diydoohickeys/Rackglow/docs/images/panel-colour.jpg

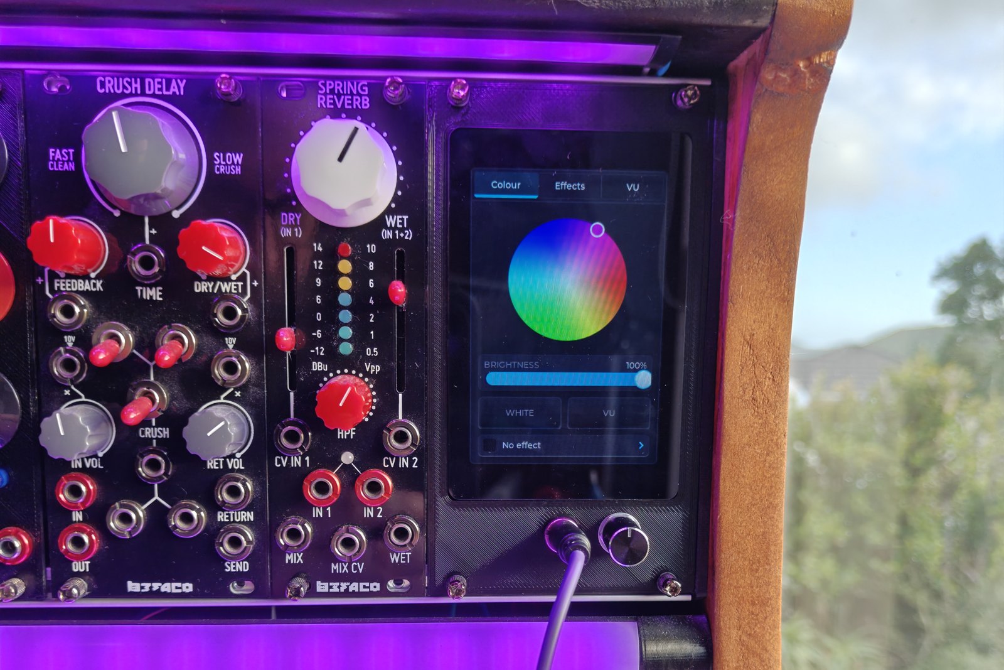
docs/images/panel-colour.jpg
