diydoohickeys/Rackglow/hardware/rackglow.kicad_sch

## KiCad design hardware/rackglow.kicad_sch (2026-09-21)

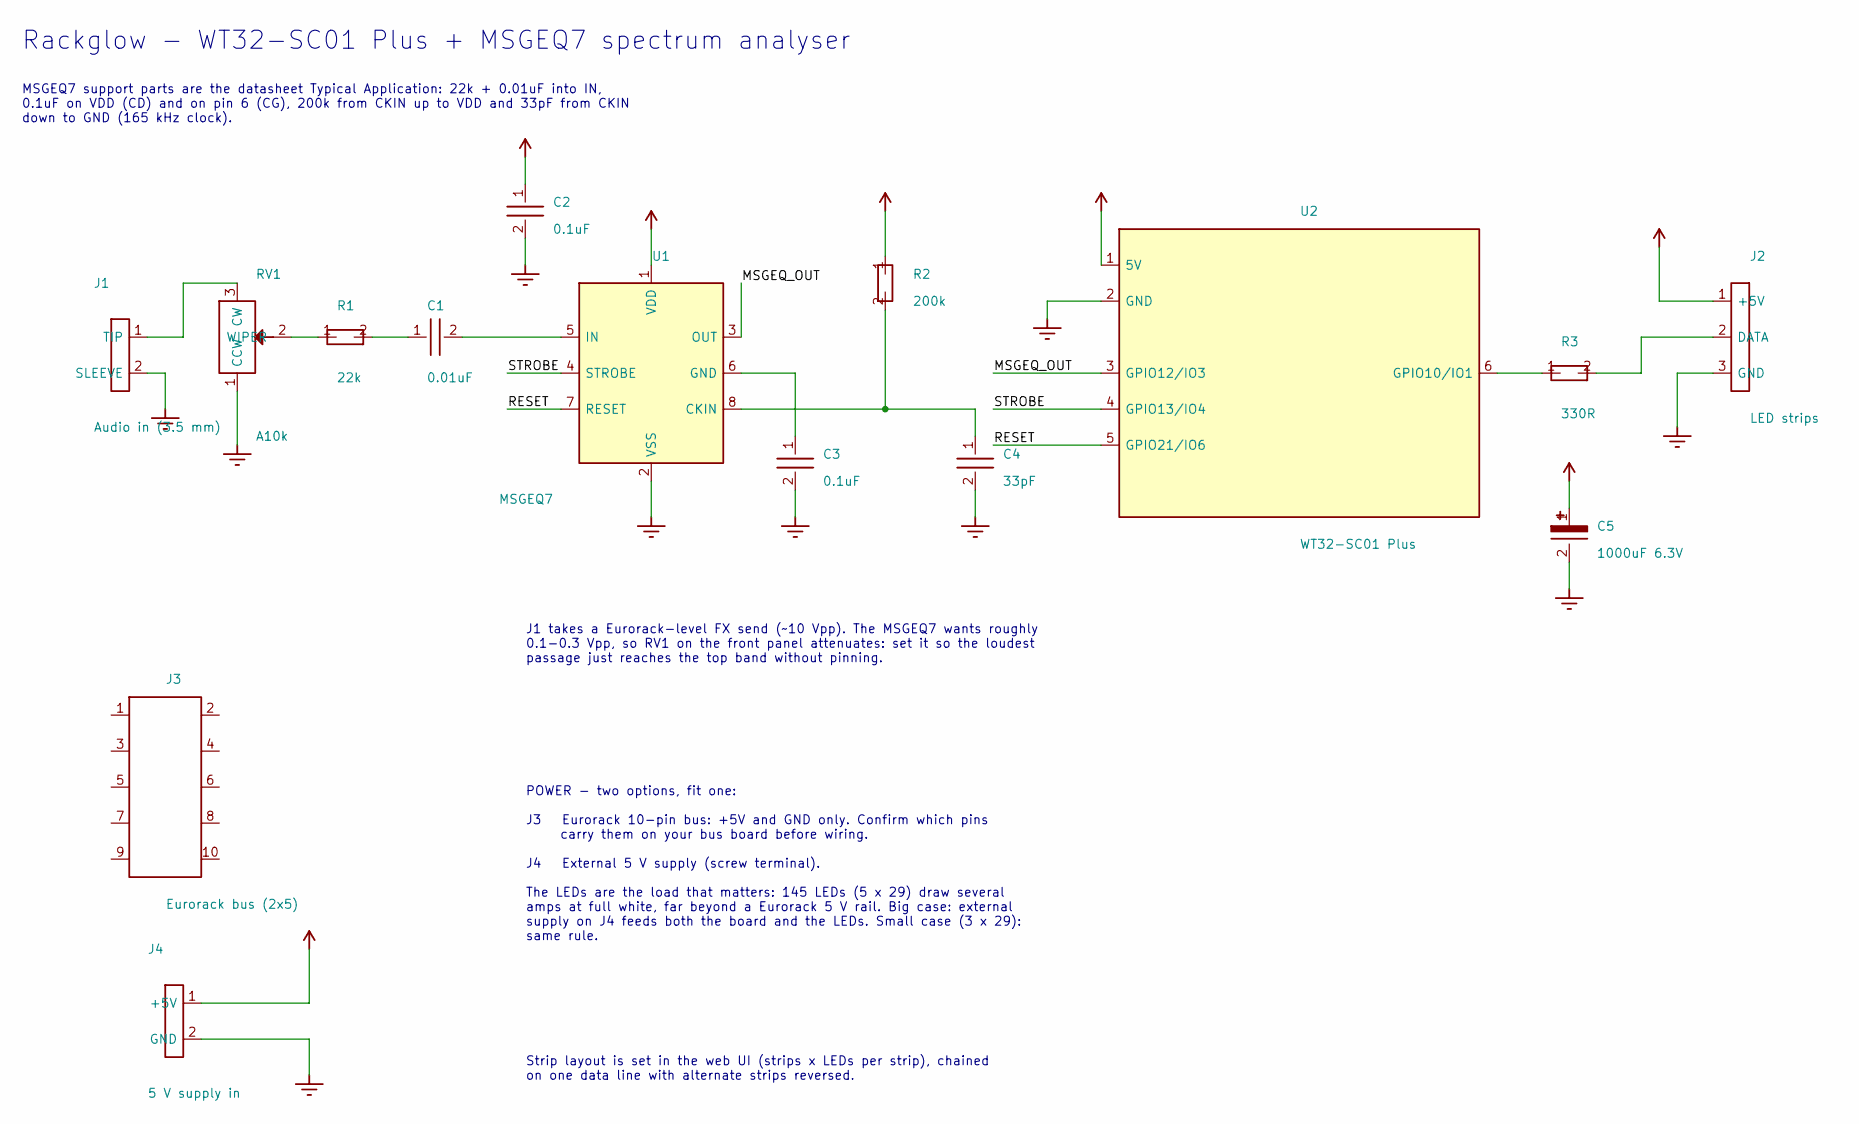
[picture p33: schematic rackglow.kicad_sch]

Parts:
C1: 0.01uF
C2, C3: 0.1uF
C4: 33pF
C5: 1000uF 6.3V
J1: Audio in (3.5 mm)
J2: LED strips
J3: Eurorack bus (2x5)
J4: 5 V supply in
R1: 22k
R2: 200k
R3: 330R
RV1: A10k
U1: MSGEQ7
U2: WT32-SC01 Plus

Connections:
+5V: C2.1, C5.1, J2.1 (+5V), J4.1 (+5V), R2.1, U1.1 (VDD), U2.1 (5V)
GND: C2.2, C3.2, C4.2, C5.2, J1.2 (SLEEVE), J2.3 (GND), J4.2 (GND), RV1.1 (CCW), U1.2 (VSS), U2.2 (GND)
MSGEQ_OUT: U1.3 (OUT), U2.3 (GPIO12/IO3)
unnamed: C1.1, R1.2
unnamed: C1.2, U1.5 (IN)
unnamed: C3.1, U1.6 (GND)
unnamed: C4.1, R2.2, U1.8 (CKIN)
unnamed: J1.1 (TIP), RV1.3 (CW)
unnamed: J2.2 (DATA), R3.2
unnamed: R1.1, RV1.2 (WIPER)
unnamed: R3.1, U2.6 (GPIO10/IO1)
RESET: U1.7 (RESET), U2.5 (GPIO21/IO6)
STROBE: U1.4 (STROBE), U2.4 (GPIO13/IO4)

Notes on the sheet:
Rackglow - WT32-SC01 Plus + MSGEQ7 spectrum analyser
MSGEQ7 support parts are the datasheet Typical Application: 22k + 0.01uF into IN, 0.1uF on VDD (CD) and on pin 6 (CG), 200k from CKIN up to VDD and 33pF from CKIN down to GND (165 kHz clock).
J1 takes a Eurorack-level FX send (~10 Vpp). The MSGEQ7 wants roughly 0.1-0.3 Vpp, so RV1 on the front panel attenuates: set it so the loudest passage just reaches the top band without pinning.
POWER - two options, fit one: J3 Eurorack 10-pin bus: +5V and GND only. Confirm which pins carry them on your bus board before wiring. J4 External 5 V supply (screw terminal). The LEDs are the load that matters: 145 LEDs (5 x 29) draw several amps at full white, far beyond a Eurorack 5 V rail. Big 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
Strip layout is set in the web UI (strips x LEDs per strip), chained on one data line with alternate strips reversed.
